YamiYukiSenpai/MacroKeyTouchSensor/index_src/IMG_20181127_023141.jpg

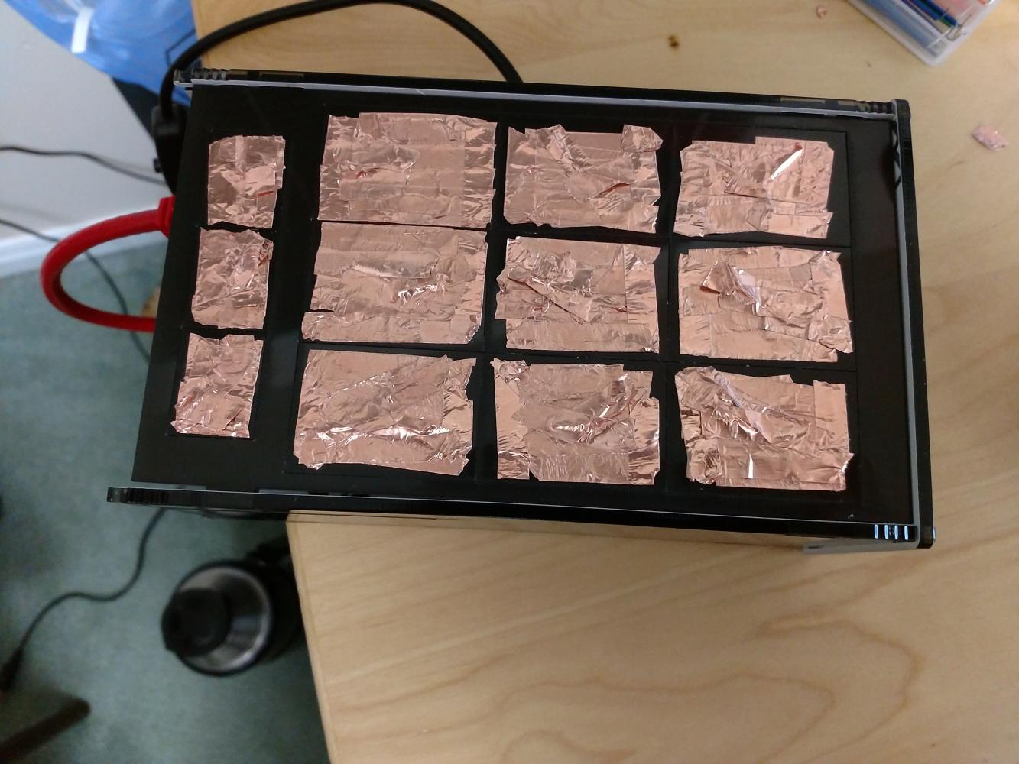
index_src/IMG_20181127_023141.jpg
